TomasD-git/MacroPad-V2/Pictures/Screenshot 2026-04-08 103510.png

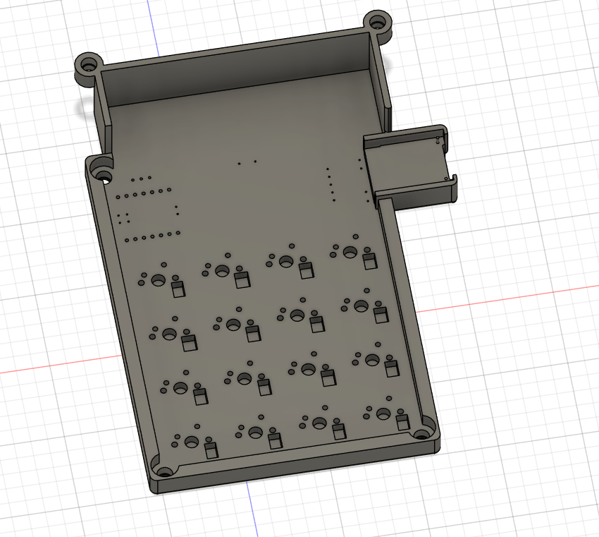
Pictures/Screenshot 2026-04-08 103510.png
